JellyTitan/ErgoDonk/ergodonk_kicad_library/3dmodels/solenoid 6V 12V 24V.png

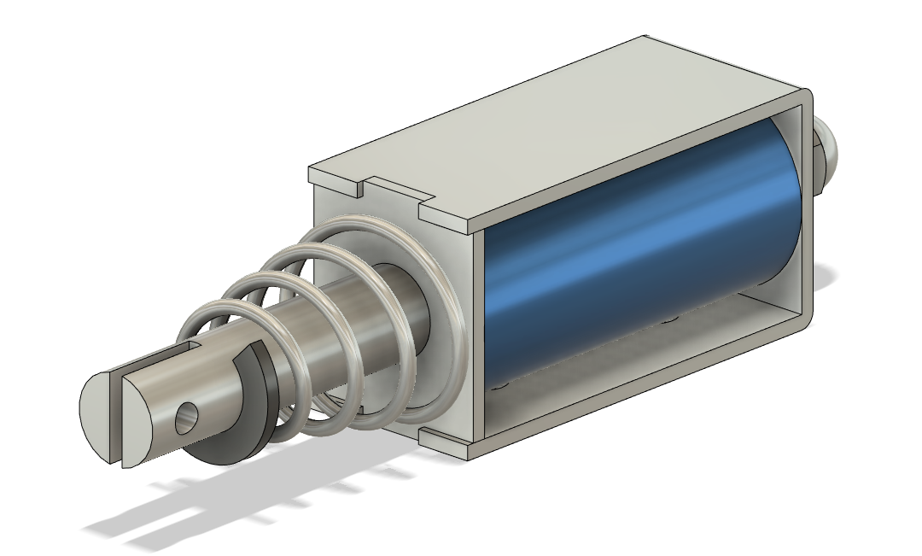
ergodonk_kicad_library/3dmodels/solenoid 6V 12V 24V.png
