JellyTitan/ErgoDonk/ergodonk_kicad_library/promicro-arduino-1.snapshot.2/Snipaste_2022-10-09_12-05-52.png

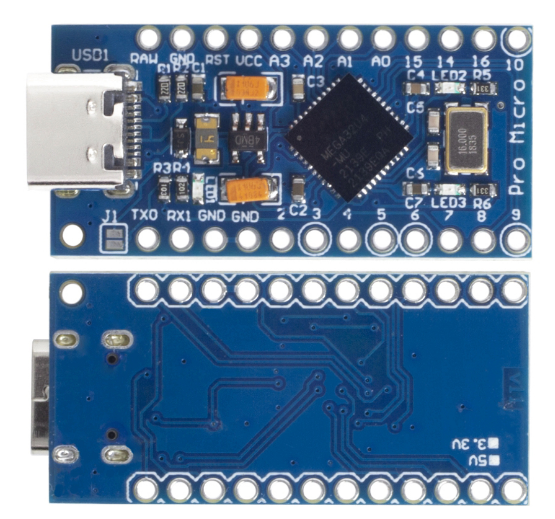
ergodonk_kicad_library/promicro-arduino-1.snapshot.2/Snipaste_2022-10-09_12-05-52.png
