JellyTitan/ErgoDonk/MS_4000_reference/7-Figure8-1.png

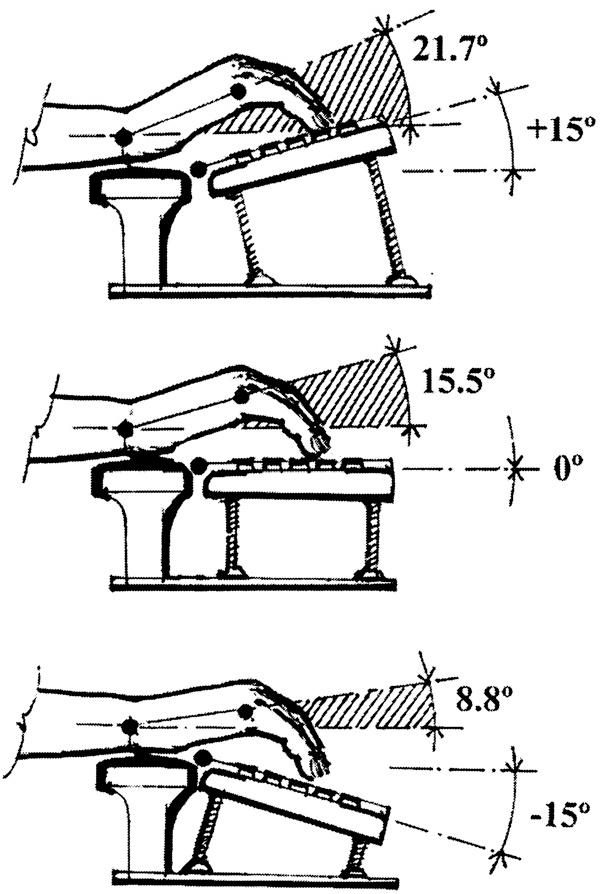
MS_4000_reference/7-Figure8-1.png
