JellyTitan/ErgoDonk/MS_4000_reference/8-Table1-1.png

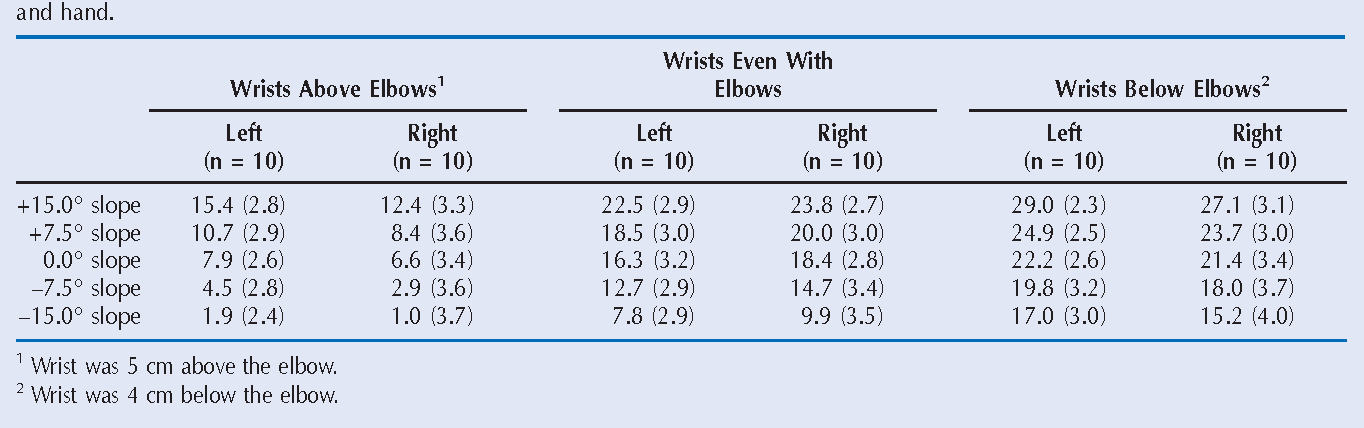
MS_4000_reference/8-Table1-1.png
