JellyTitan/ErgoDonk/MS_4000_reference/microsoft_natural_ergo_keyboard_4000_p3_358x228.jpeg

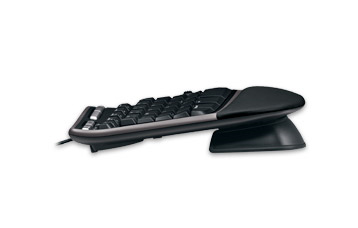
MS_4000_reference/microsoft_natural_ergo_keyboard_4000_p3_358x228.jpeg
