JellyTitan/ErgoDonk/reference_images/hp_gold_star.png

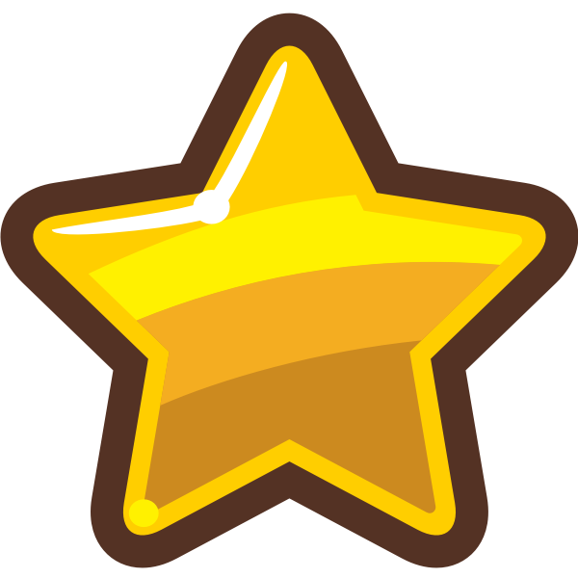
reference_images/hp_gold_star.png
