JellyTitan/ErgoDonk/reference_images/star.png

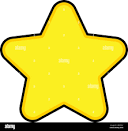
reference_images/star.png
