JellyTitan/ErgoDonk/Ergodonk blackpill wiring diagram.png

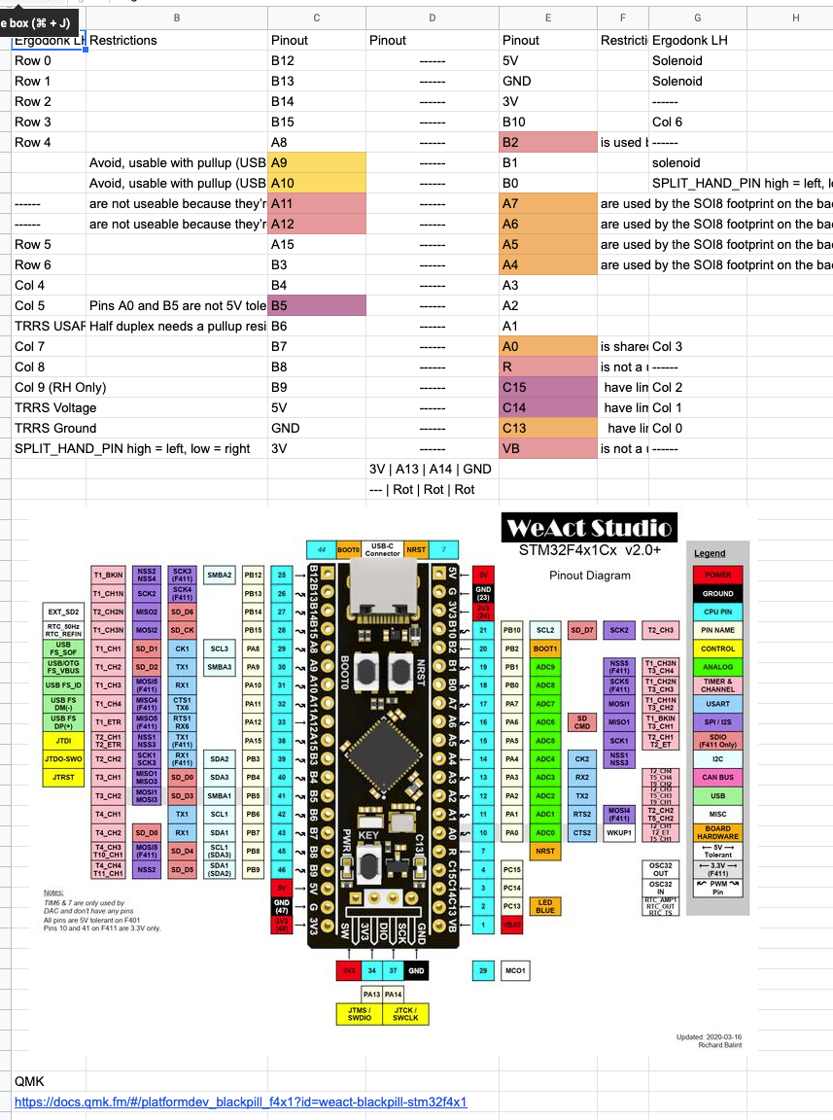
Ergodonk blackpill wiring diagram.png
