JellyTitan/ErgoDonk/kbfirmware_wiring_diagrams/V2/Ergodonk_LH_wiring_diagram_V2.png

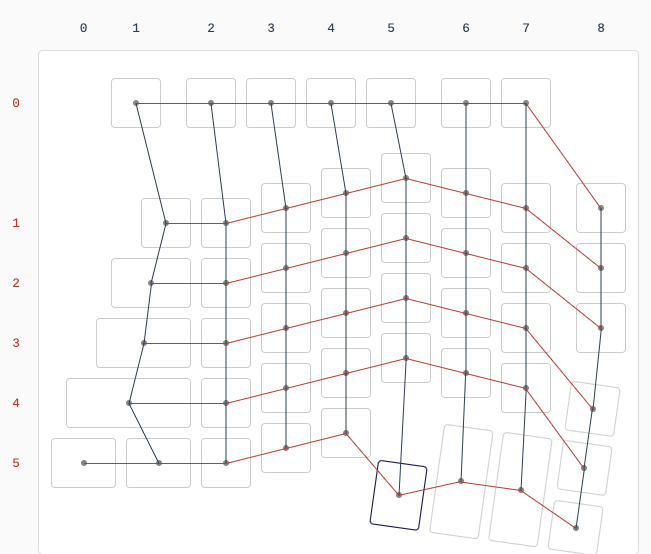
kbfirmware_wiring_diagrams/V2/Ergodonk_LH_wiring_diagram_V2.png
