JellyTitan/ErgoDonk/kbfirmware_wiring_diagrams/V2/Ergodonk_RH_wiring_diagram_V2.png

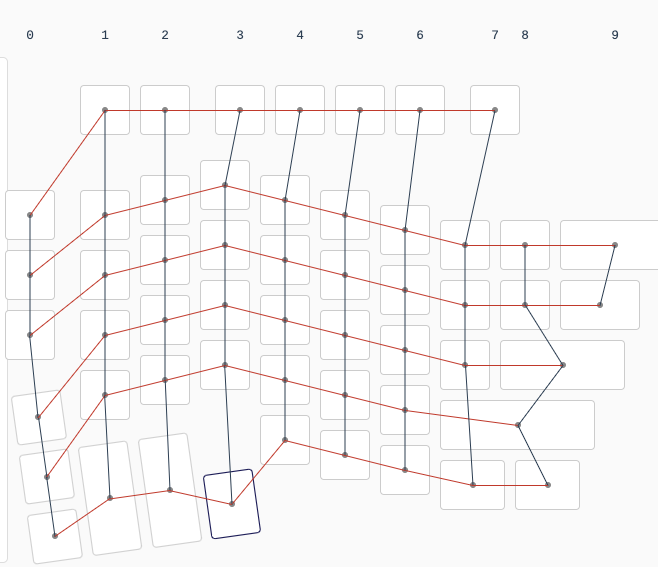
kbfirmware_wiring_diagrams/V2/Ergodonk_RH_wiring_diagram_V2.png
