JellyTitan/ErgoDonk/kbfirmware_wiring_diagrams/V2/Ergodonk_RH_wiring_diagram_V2c.png

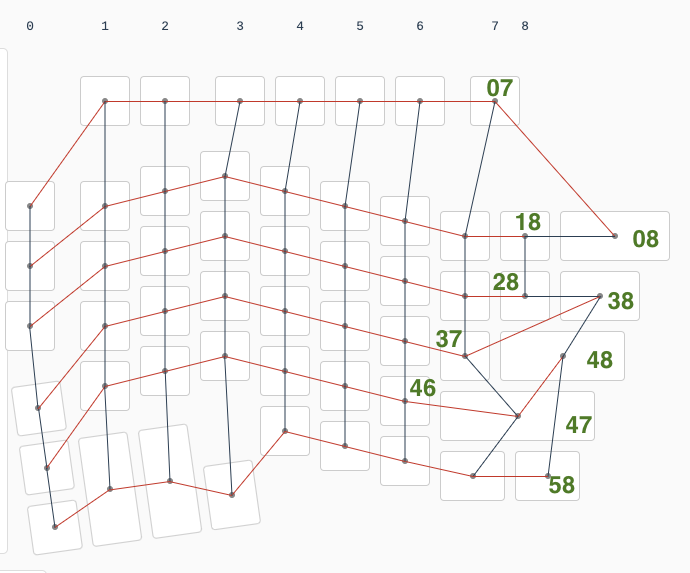
kbfirmware_wiring_diagrams/V2/Ergodonk_RH_wiring_diagram_V2c.png
