JellyTitan/ErgoDonk/reference_images/trrs wiring.jpeg

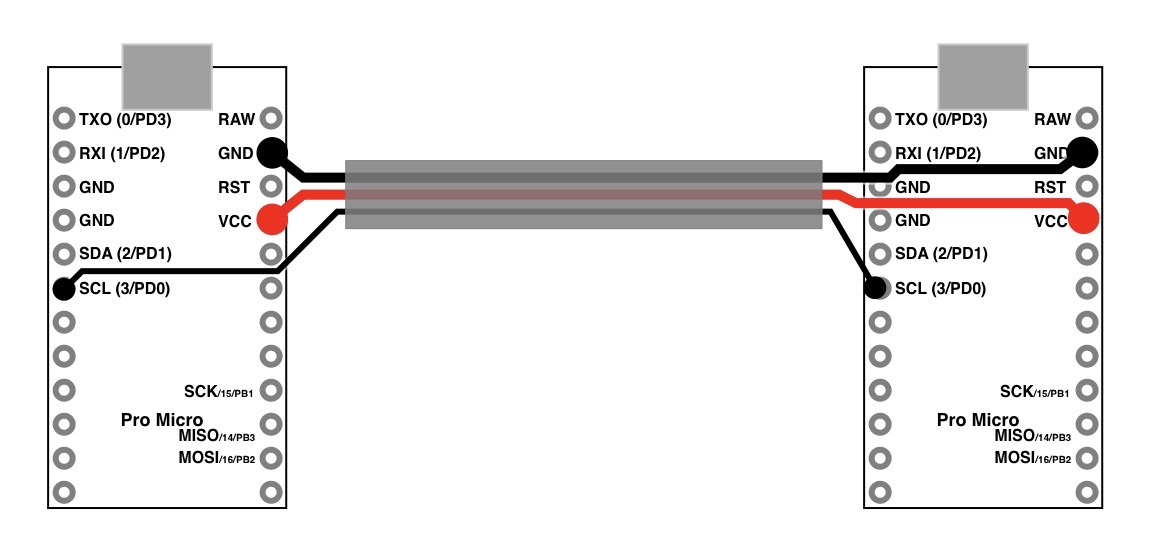
reference_images/trrs wiring.jpeg
