JellyTitan/ErgoDonk/ergodonk_ds_oled/ergodonk_ds_oled/ergodonk_ds_oled.kicad_sch

## KiCad design ergodonk_ds_oled/ergodonk_ds_oled/ergodonk_ds_oled.kicad_sch (2023-07-13)

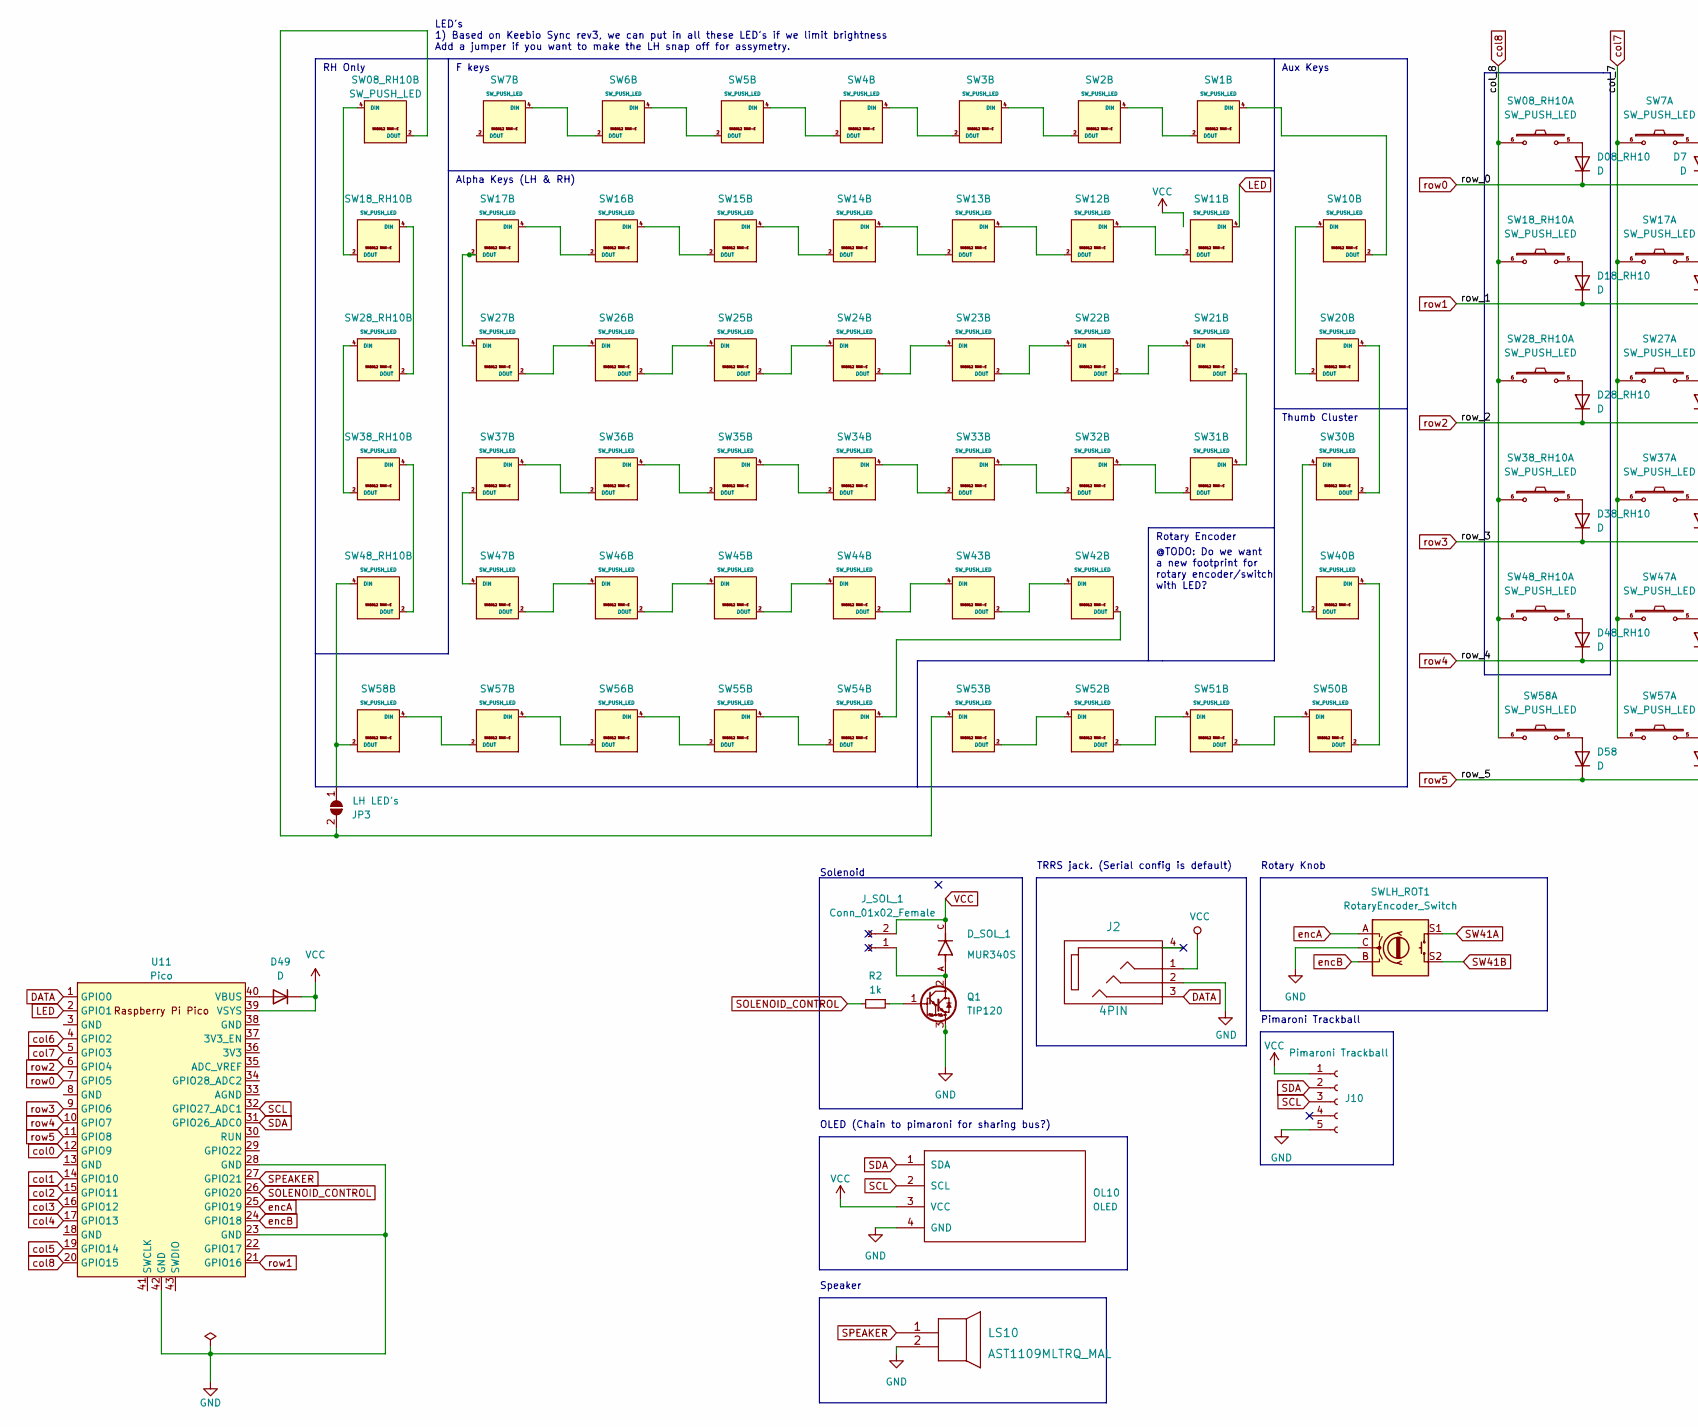
[picture p53: schematic ergodonk_ds_oled.kicad_sch, part in row 1, column 1]

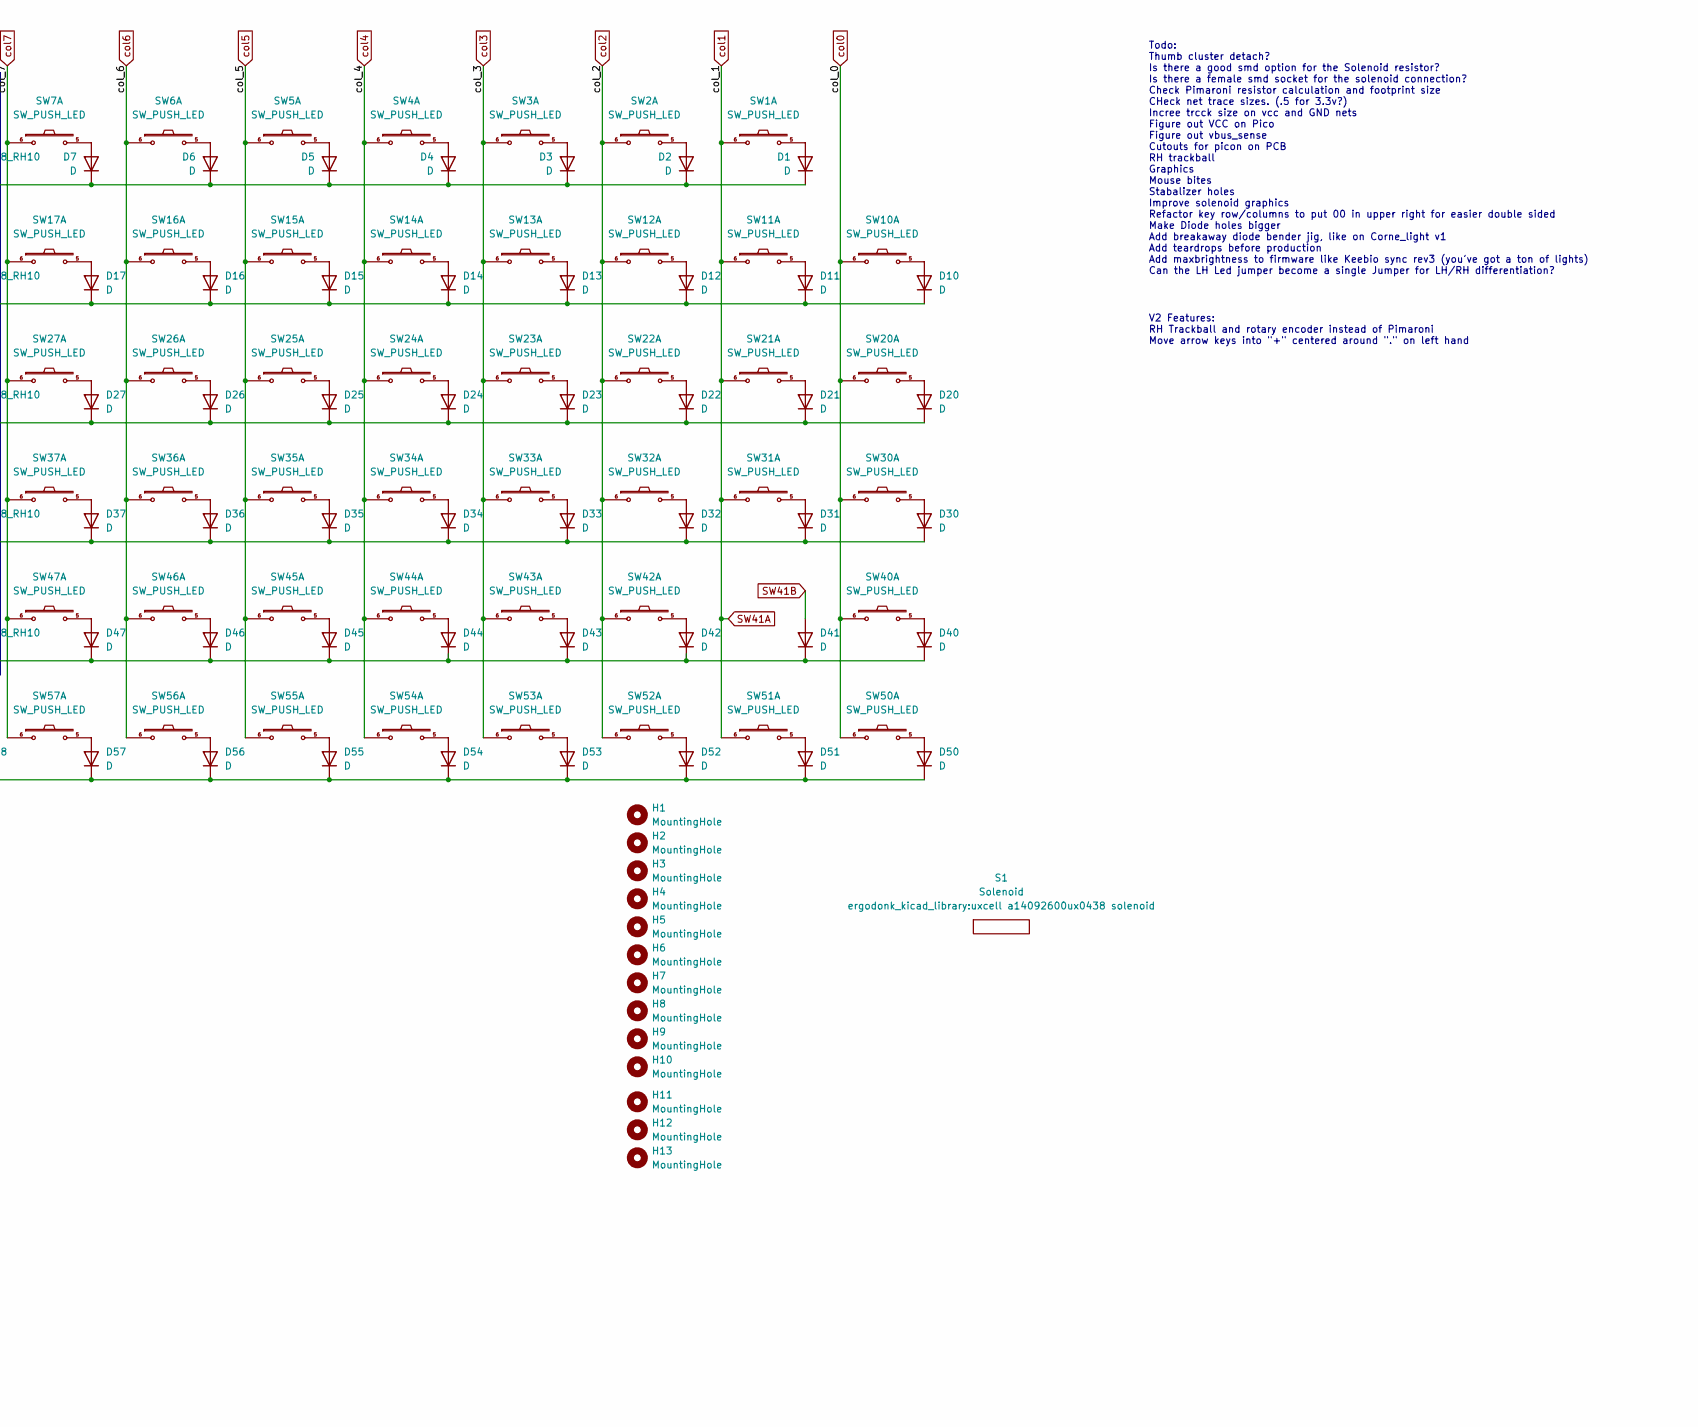
[picture p54: schematic ergodonk_ds_oled.kicad_sch, part in row 1, column 2]

Parts:
D1, D2, D3, D4, D5, D6, D7, D08_RH10, D10, D11, D12, D13, D14, D15, D16, D17, D18_RH10, D20, D21, D22, D23, D24, D25, D26, D27, D28_RH10, D30, D31, D32, D33, D34, D35, D36, D37, D38_RH10, D40, D41, D42, D43, D44, D45, D46, D47, D48_RH10, D50, D51, D52, D53, D54, D55, D56, D57, D58: D; D_SOD-123_DO-35_Hybrid_DoubleSided
D49: D; D3_TH_SMD_v2
D_SOL_1: MUR340S; MUR340S_IN4001_TH_HYBRID; PARTREV L2102
H1, H2, H3, H4, H5, H6, H7, H8, H9, H10, H11, H12, H13: MountingHole; MountingHole_2.2mm_M2_Pad_Via
J2: 4PIN; MJ-4PP-9_CANTOR_KITCHEN_SINK
J10: Pimaroni Trackball; pimoroni_trackball
JP3: LH LED's; PinHeader_1x02_P2.54mm_Vertical
J_SOL_1: Conn_01x02_Female; PinHeader_1x02_P2.54mm_Vertical
LS10: AST1109MLTRQ_MAL; AST1109MLTRQ
OL10: OLED; OLED SSD1306 128x64 UNVERIFIED v2
Q1: TIP120; Tip 120 with heatsink
R2: 1k; R_Axial_DIN0309_L9.0mm_D3.2mm_P12.70mm_Horizontal
S1: Solenoid; uxcell a14092600ux0438 solenoid
SW1, SW2, SW3, SW4, SW5, SW6, SW7, SW10, SW11, SW12, SW13, SW14, SW15, SW16, SW17, SW20, SW21, SW22, SW23, SW24, SW25, SW26, SW30, SW31, SW32, SW33, SW34, SW35, SW36, SW40, SW42, SW43, SW44, SW45, SW46, SW50, SW51, SW52, SW53, SW54, SW55, SW56, SW57, SW58: SW_PUSH_LED; Cherry_MX_DS_Hotswap_miniE_1U_sofle3b v2
SW08_RH10: SW_PUSH_LED; V2_CherryMX_DoubleSided_Hotswap_miniE_2u_RH_ONLY
SW18_RH10: SW_PUSH_LED; Cherry_MX_DS_Hotswap_miniE_1U_sofle3b_oneside
SW27: SW_PUSH_LED; V2_CherryMX_DoubleSided_Hotswap_miniE_1.5u_LH_1u_RH
SW28_RH10: SW_PUSH_LED; V2_CherryMX_DoubleSided_Hotswap_miniE_1.5u_RH_ONLY
SW37: SW_PUSH_LED; V2_CherryMX_DoubleSided_Hotswap_miniE_1.75u_LH_1u_RH
SW38_RH10: SW_PUSH_LED; V2_CherryMX_DS_Hotswap_miniE_1U_SEED_RH
SW47: SW_PUSH_LED; V2_CherryMX_DoubleSided_Hotswap_miniE_2.25u_LH_2.75u_RH
SW48_RH10: SW_PUSH_LED; V2_CherryMX_DoubleSided_Hotswap_miniE_2.25u_RH_ONLY
SWLH_ROT1: RotaryEncoder_Switch; RotaryEncoder_EC11_ergodonk_variant
U11: Pico; RPi_Pico_SMD_TH - Junco -DS Sofle v3b v4

Connections:
DATA: J2.3, U11.1 (GPIO0)
GND: J2.2, J10.5, LS10.2, OL10.4 (GND), Q1.3 (E), SWLH_ROT1.C, U11.23 (GND), U11.28 (GND), U11.42 (GND)
LED: SW11.4 (DIN), U11.2 (GPIO1)
unnamed: D1.2 (A), SW1.5
unnamed: D2.2 (A), SW2.5
unnamed: D3.2 (A), SW3.5
unnamed: D4.2 (A), SW4.5
unnamed: D5.2 (A), SW5.5
unnamed: D6.2 (A), SW6.5
unnamed: D7.2 (A), SW7.5
unnamed: D08_RH10.2 (A), SW08_RH10.5
unnamed: D10.2 (A), SW10.5
unnamed: D11.2 (A), SW11.5
unnamed: D12.2 (A), SW12.5
unnamed: D13.2 (A), SW13.5
unnamed: D14.2 (A), SW14.5
unnamed: D15.2 (A), SW15.5
unnamed: D16.2 (A), SW16.5
unnamed: D17.2 (A), SW17.5
unnamed: D18_RH10.2 (A), SW18_RH10.5
unnamed: D20.2 (A), SW20.5
unnamed: D21.2 (A), SW21.5
unnamed: D22.2 (A), SW22.5
unnamed: D23.2 (A), SW23.5
unnamed: D24.2 (A), SW24.5
unnamed: D25.2 (A), SW25.5
unnamed: D26.2 (A), SW26.5
unnamed: D27.2 (A), SW27.5
unnamed: D28_RH10.2 (A), SW28_RH10.5
unnamed: D30.2 (A), SW30.5
unnamed: D31.2 (A), SW31.5
unnamed: D32.2 (A), SW32.5
unnamed: D33.2 (A), SW33.5
unnamed: D34.2 (A), SW34.5
unnamed: D35.2 (A), SW35.5
unnamed: D36.2 (A), SW36.5
unnamed: D37.2 (A), SW37.5
unnamed: D38_RH10.2 (A), SW38_RH10.5
unnamed: D40.2 (A), SW40.5
unnamed: D42.2 (A), SW42.5
unnamed: D43.2 (A), SW43.5
unnamed: D44.2 (A), SW44.5
unnamed: D45.2 (A), SW45.5
unnamed: D46.2 (A), SW46.5
unnamed: D47.2 (A), SW47.5
unnamed: D48_RH10.2 (A), SW48_RH10.5
unnamed: D49.2 (A), U11.40 (VBUS)
unnamed: D50.2 (A), SW50.5
unnamed: D51.2 (A), SW51.5
unnamed: D52.2 (A), SW52.5
unnamed: D53.2 (A), SW53.5
unnamed: D54.2 (A), SW54.5
unnamed: D55.2 (A), SW55.5
unnamed: D56.2 (A), SW56.5
unnamed: D57.2 (A), SW57.5
unnamed: D58.2 (A), SW58.5
unnamed: D_SOL_1.A, J_SOL_1.1, Q1.2 (C)
unnamed: JP3.1 (A), SW48_RH10.4 (DIN), SW58.2 (DOUT)
unnamed: JP3.2 (B), SW08_RH10.2 (DOUT), SW53.4 (DIN)
unnamed: Q1.1 (B), R2.1
unnamed: SW1.2 (DOUT), SW2.4 (DIN)
unnamed: SW1.4 (DIN), SW10.2 (DOUT)
unnamed: SW2.2 (DOUT), SW3.4 (DIN)
unnamed: SW3.2 (DOUT), SW4.4 (DIN)
unnamed: SW4.2 (DOUT), SW5.4 (DIN)
unnamed: SW5.2 (DOUT), SW6.4 (DIN)
unnamed: SW6.2 (DOUT), SW7.4 (DIN)
unnamed: SW08_RH10.4 (DIN), SW18_RH10.2 (DOUT)
unnamed: SW10.4 (DIN), SW20.2 (DOUT)
unnamed: SW11.2 (DOUT), SW12.4 (DIN)
unnamed: SW12.2 (DOUT), SW13.4 (DIN)
unnamed: SW13.2 (DOUT), SW14.4 (DIN)
unnamed: SW14.2 (DOUT), SW15.4 (DIN)
unnamed: SW15.2 (DOUT), SW16.4 (DIN)
unnamed: SW16.2 (DOUT), SW17.4 (DIN)
unnamed: SW17.2 (DOUT), SW27.4 (DIN)
unnamed: SW18_RH10.4 (DIN), SW28_RH10.2 (DOUT)
unnamed: SW20.4 (DIN), SW30.2 (DOUT)
unnamed: SW21.2 (DOUT), SW31.4 (DIN)
unnamed: SW21.4 (DIN), SW22.2 (DOUT)
unnamed: SW22.4 (DIN), SW23.2 (DOUT)
unnamed: SW23.4 (DIN), SW24.2 (DOUT)
unnamed: SW24.4 (DIN), SW25.2 (DOUT)
unnamed: SW25.4 (DIN), SW26.2 (DOUT)
unnamed: SW26.4 (DIN), SW27.2 (DOUT)
unnamed: SW28_RH10.4 (DIN), SW38_RH10.2 (DOUT)
unnamed: SW30.4 (DIN), SW40.2 (DOUT)
unnamed: SW31.2 (DOUT), SW32.4 (DIN)
unnamed: SW32.2 (DOUT), SW33.4 (DIN)
unnamed: SW33.2 (DOUT), SW34.4 (DIN)
unnamed: SW34.2 (DOUT), SW35.4 (DIN)
unnamed: SW35.2 (DOUT), SW36.4 (DIN)
unnamed: SW36.2 (DOUT), SW37.4 (DIN)
unnamed: SW37.2 (DOUT), SW47.4 (DIN)
unnamed: SW38_RH10.4 (DIN), SW48_RH10.2 (DOUT)
unnamed: SW40.4 (DIN), SW50.2 (DOUT)
unnamed: SW42.2 (DOUT), SW54.4 (DIN)
unnamed: SW42.4 (DIN), SW43.2 (DOUT)
unnamed: SW43.4 (DIN), SW44.2 (DOUT)
unnamed: SW44.4 (DIN), SW45.2 (DOUT)
unnamed: SW45.4 (DIN), SW46.2 (DOUT)
unnamed: SW46.4 (DIN), SW47.2 (DOUT)
unnamed: SW50.4 (DIN), SW51.2 (DOUT)
unnamed: SW51.4 (DIN), SW52.2 (DOUT)
unnamed: SW52.4 (DIN), SW53.2 (DOUT)
unnamed: SW54.2 (DOUT), SW55.4 (DIN)
unnamed: SW55.2 (DOUT), SW56.4 (DIN)
unnamed: SW56.2 (DOUT), SW57.4 (DIN)
unnamed: SW57.2 (DOUT), SW58.4 (DIN)
SCL: J10.3, OL10.2 (SCL), U11.32 (GPIO27_ADC1)
SDA: J10.2, OL10.1 (SDA), U11.31 (GPIO26_ADC0)
SOLENOID_CONTROL: R2.2, U11.26 (GPIO20)
SPEAKER: LS10.1, U11.27 (GPIO21)
SW41B: D41.2 (A), SWLH_ROT1.S2
VCC: D49.1 (K), D_SOL_1.C, J2.1, J10.1, J_SOL_1.2, OL10.3 (VCC), SW11.1 (VDD), U11.39 (VSYS)
col0: SW10.6, SW20.6, SW30.6, SW40.6, SW50.6, U11.12 (GPIO9)
col1: SW1.6, SW11.6, SW21.6, SW31.6, SW51.6, SWLH_ROT1.S1, U11.14 (GPIO10)
col2: SW2.6, SW12.6, SW22.6, SW32.6, SW42.6, SW52.6, U11.15 (GPIO11)
col3: SW3.6, SW13.6, SW23.6, SW33.6, SW43.6, SW53.6, U11.16 (GPIO12)
col4: SW4.6, SW14.6, SW24.6, SW34.6, SW44.6, SW54.6, U11.17 (GPIO13)
col5: SW5.6, SW15.6, SW25.6, SW35.6, SW45.6, SW55.6, U11.19 (GPIO14)
col6: SW6.6, SW16.6, SW26.6, SW36.6, SW46.6, SW56.6, U11.4 (GPIO2)
col7: SW7.6, SW17.6, SW27.6, SW37.6, SW47.6, SW57.6, U11.5 (GPIO3)
col8: SW08_RH10.6, SW18_RH10.6, SW28_RH10.6, SW38_RH10.6, SW48_RH10.6, SW58.6, U11.20 (GPIO15)
encA: SWLH_ROT1.A, U11.25 (GPIO19)
encB: SWLH_ROT1.B, U11.24 (GPIO18)
row0: D1.1 (K), D2.1 (K), D3.1 (K), D4.1 (K), D5.1 (K), D6.1 (K), D7.1 (K), D08_RH10.1 (K), U11.7 (GPIO5)
row1: D10.1 (K), D11.1 (K), D12.1 (K), D13.1 (K), D14.1 (K), D15.1 (K), D16.1 (K), D17.1 (K), D18_RH10.1 (K), U11.21 (GPIO16)
row2: D20.1 (K), D21.1 (K), D22.1 (K), D23.1 (K), D24.1 (K), D25.1 (K), D26.1 (K), D27.1 (K), D28_RH10.1 (K), U11.6 (GPIO4)
row3: D30.1 (K), D31.1 (K), D32.1 (K), D33.1 (K), D34.1 (K), D35.1 (K), D36.1 (K), D37.1 (K), D38_RH10.1 (K), U11.9 (GPIO6)
row4: D40.1 (K), D41.1 (K), D42.1 (K), D43.1 (K), D44.1 (K), D45.1 (K), D46.1 (K), D47.1 (K), D48_RH10.1 (K), U11.10 (GPIO7)
row5: D50.1 (K), D51.1 (K), D52.1 (K), D53.1 (K), D54.1 (K), D55.1 (K), D56.1 (K), D57.1 (K), D58.1 (K), U11.11 (GPIO8)

Notes on the sheet:
Todo: Thumb cluster detach? Is there a good smd option for the Solenoid resistor? Is there a female smd socket for the solenoid connection? Check Pimaroni resistor calculation and footprint size CHeck net trace sizes. (.5 for 3.3v?) Incree trcck size on vcc and GND nets Figure out VCC on Pico Figur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
Speaker
Aux Keys
Thumb Cluster
Pimaroni Trackball
Solenoid
@TODO: Do we want a new footprint for rotary encoder/switch with LED?
RH Only
Alpha Keys (LH & RH)
LED's 1) Based on Keebio Sync rev3, we can put in all these LED's if we limit brightness Add a jumper if you want to make the LH snap off for assymetry.
OLED (Chain to pimaroni for sharing bus?)
V2 Features: RH Trackball and rotary encoder instead of Pimaroni Move arrow keys into "+" centered around "." on left hand
F keys
TRRS jack. (Serial config is default)
Rotary Encoder
Rotary Knob
